SteMaker/wortuhr/pics/anschluss_ftdi.jpg

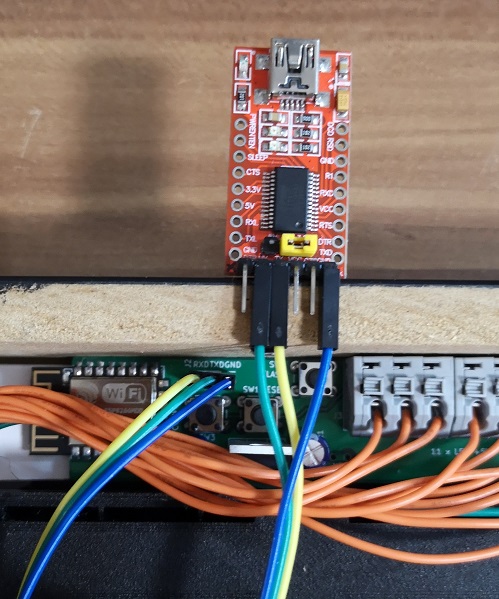
pics/anschluss_ftdi.jpg
