SteMaker/wortuhr/pics/gitter_und_platine.jpg

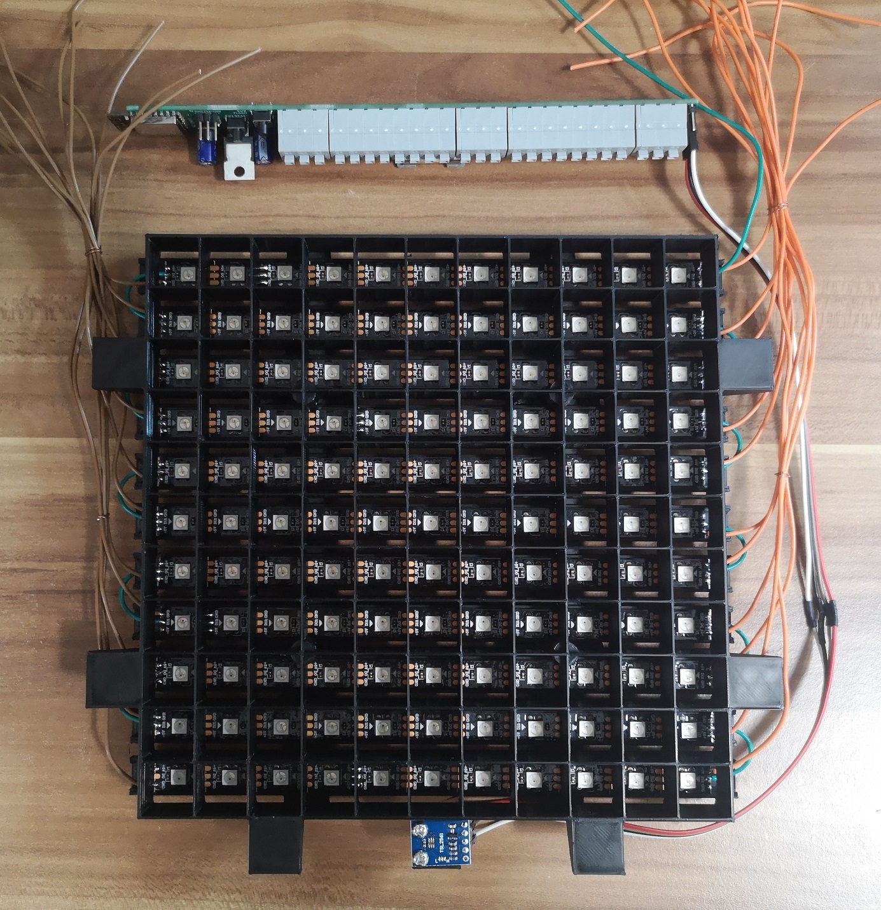
pics/gitter_und_platine.jpg
