SteMaker/wortuhr/pics/pio_upload.png

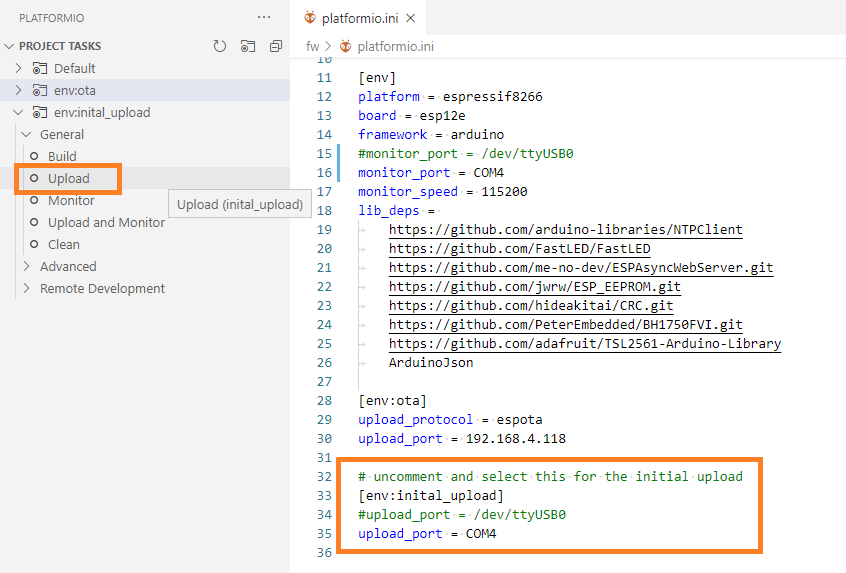
pics/pio_upload.png
