SteMaker/wortuhr/pics/platzierung.jpg

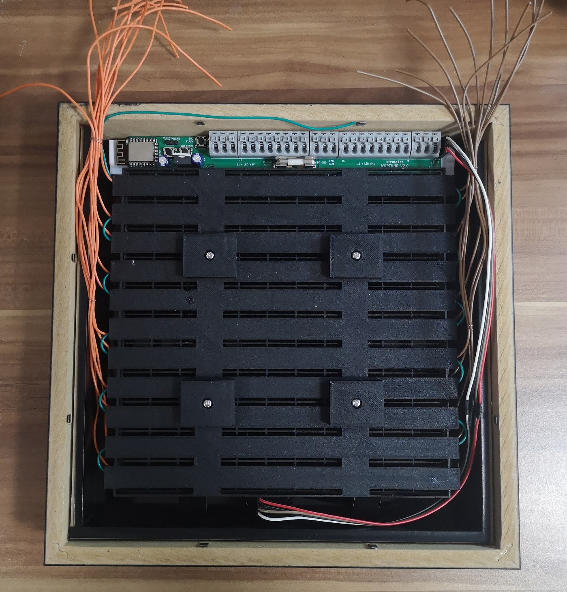
pics/platzierung.jpg
