SteMaker/wortuhr/pics/platzierung_platine.jpg

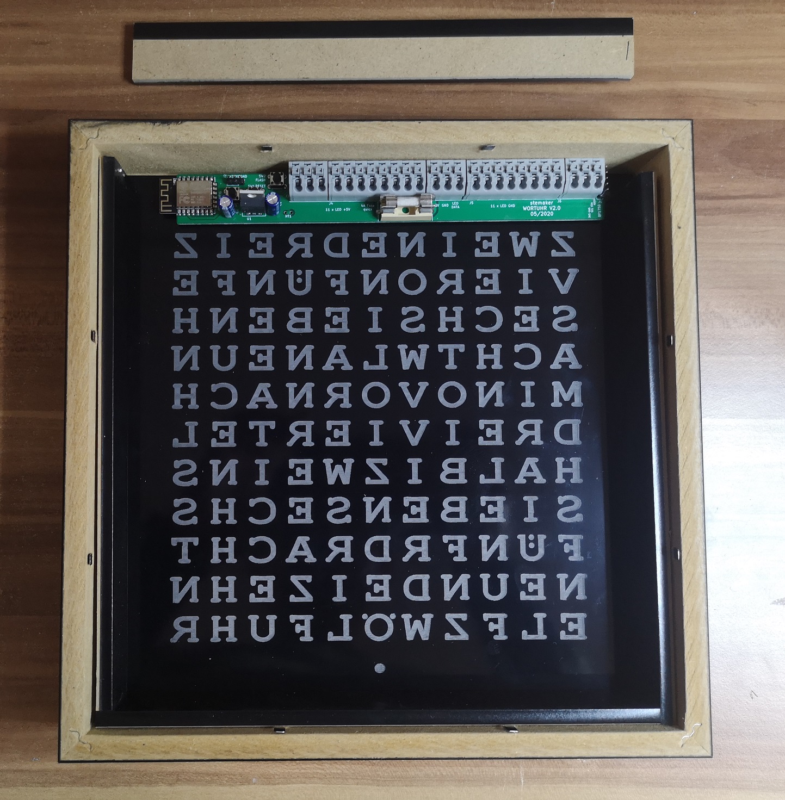
pics/platzierung_platine.jpg
