SteMaker/wortuhr/pics/platzierung_platine_detail.jpg

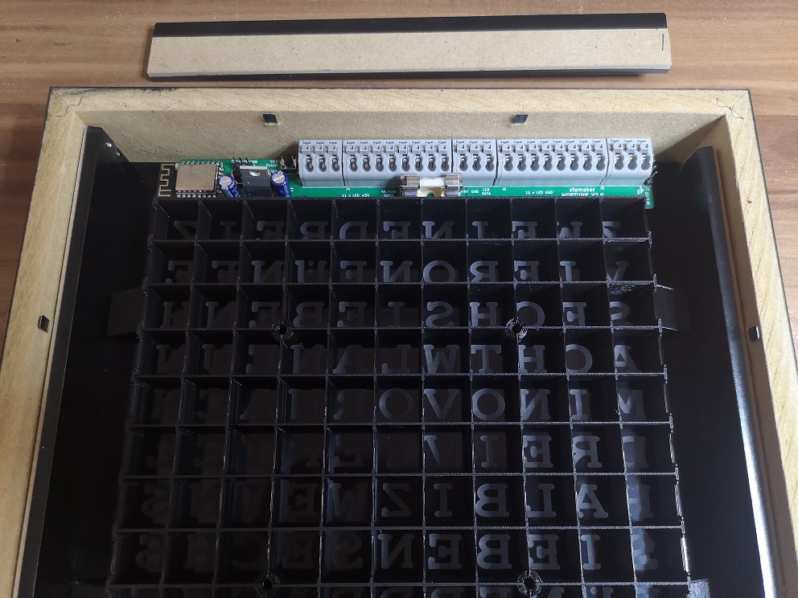
pics/platzierung_platine_detail.jpg
