SteMaker/wortuhr/pics/rueckseite_bedrahtet.jpg

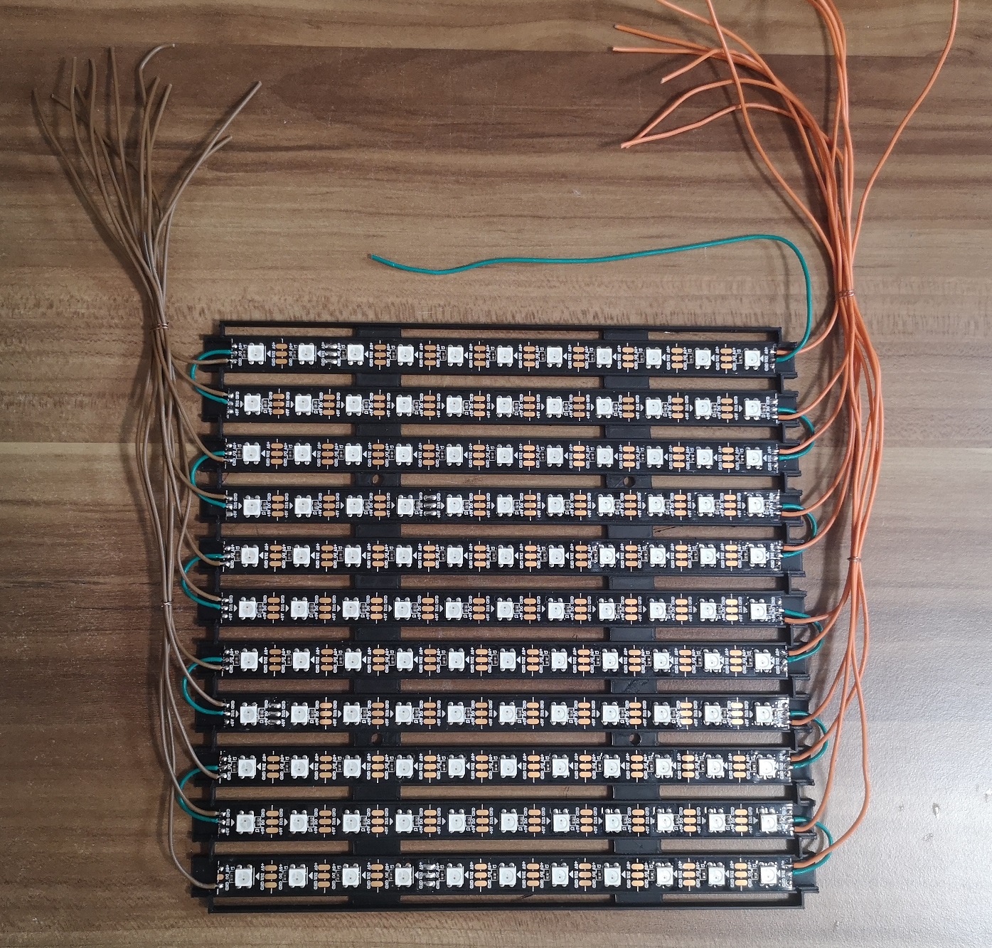
pics/rueckseite_bedrahtet.jpg
