SteMaker/wortuhr/pics/rueckseite_einbau_led.jpg

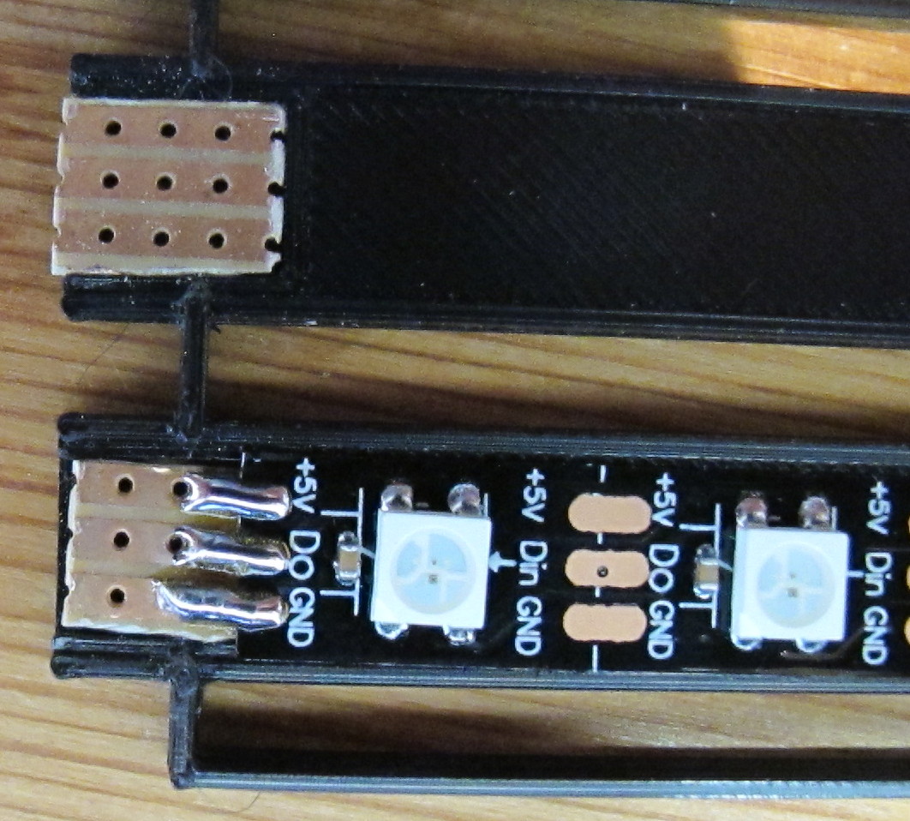
pics/rueckseite_einbau_led.jpg
