SteMaker/wortuhr/pics/zusammenbau_komplett.jpg

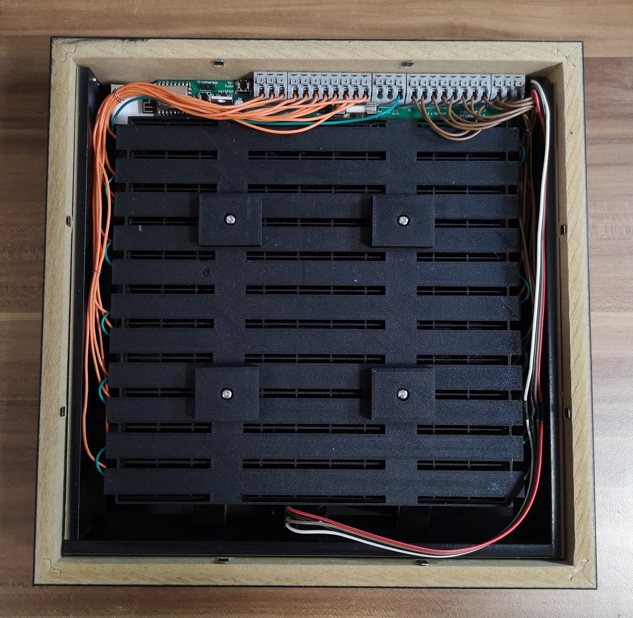
pics/zusammenbau_komplett.jpg
